jrowberg/keyglove/controller/arduino/keyglove/keyglove.cpp

// Keyglove Controller source code - Main setup/loop controller implementations
// 2015-07-03 by Jeff Rowberg <jeff@rowberg.net>

/* ============================================
Controller code is placed under the MIT license
Copyright (c) 2015 Jeff Rowberg

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
THE SOFTWARE IS PROVIDED "AS IS", WITHOUT WARRANTY OF ANY KIND, EXPRESS OR
IMPLIED, INCLUDING BUT NOT LIMITED TO THE WARRANTIES OF MERCHANTABILITY,
FITNESS FOR A PARTICULAR PURPOSE AND NONINFRINGEMENT. IN NO EVENT SHALL THE
AUTHORS OR COPYRIGHT HOLDERS BE LIABLE FOR ANY CLAIM, DAMAGES OR OTHER
LIABILITY, WHETHER IN AN ACTION OF CONTRACT, TORT OR OTHERWISE, ARISING FROM,
OUT OF OR IN CONNECTION WITH THE SOFTWARE OR THE USE OR OTHER DEALINGS IN
THE SOFTWARE.
===============================================
*/

/**
 * @file keyglove.cpp
 * @brief Main setup/loop controller implementations
 * @author Jeff Rowberg
 * @date 2015-07-03
 *
 * This is the main entry point and program flow control code for the entire
 * Keyglove Arduino firmware project, including the setup() and loop()
 * functions.
 *
 * Normally it is not necessary to edit this file.
 */

// CORE
#include "keyglove.h"

// BOARD
#include "support_board.h"

// COMMUNICATION PROTOCOL
#include "support_protocol.h"

// TOUCH SENSOR DETECTION LOGIC
#include "support_touch.h"

// FEEDBACK
#if (KG_FEEDBACK > 0)
    #include "support_feedback.h"
#endif

// MOTION
#if (KG_MOTION > 0)
    #include "support_motion.h"
#endif

// BLUETOOTH SUPPORT
#if (KG_HOSTIF & HG_HOSTIF_BT2_SPP) || (KG_HOSTIF & KG_HOSTIF_BT2_HID) || (KG_HOSTIF & KG_HOSTIF_BT2_RAWHID) || (KG_HOSTIF & KG_HOSTIF_BT2_IAP)
    #include "support_bluetooth.h"
#endif

// HUMAN INPUT DEVICE
#if (KG_HID & KG_HID_KEYBOARD)
    #include "support_hid_keyboard.h"
#endif
#if (KG_HID & KG_HID_MOUSE)
    #include "support_hid_mouse.h"
#endif

// USE THIS FILE TO IMPLEMENT ANY AUTONOMOUS BEHAVIOUR, SUCH AS ENABLING BLUETOOTH ON BOOT
#include "application.h"

volatile uint8_t keyglove100Hz = 0;         ///< Flag for 100Hz hardware timer interrupt
uint8_t keygloveTick = 0;                   ///< Fast 100Hz counter, increments every ~10ms and loops at 100
uint32_t keygloveTock = 0;                  ///< Slow 1Hz counter (a.k.a. "uptime"), increments every 100 ticks and loops at 2^32 (~4 billion)
//uint32_t keygloveTickTime = 0;              ///< Benchmark testing "end" reference timestamp
//uint32_t keygloveTickTime0 = 0;             ///< Benchmark testing "start" reference timestamp

uint8_t keygloveSoftTimers = 0;             ///< Bitmask for defined scheduled timers (one-shot or repeating)
uint8_t keygloveSoftTimersRepeat = 0;       ///< Bitmask for which scheduled timers are repeating
uint16_t keygloveSoftTimerInterval[8];      ///< Interval for each defined timer (units are 10ms)
uint32_t keygloveSoftTimerSec[8];           ///< Next "second" (tock) to execute each timer
uint8_t keygloveSoftTimer10ms[8];           ///< Next 10ms (tick) to execute each timer (w/corresponding second)

volatile uint8_t keygloveBatteryInterrupt;  ///< Flag for battery status change interrupt
volatile uint8_t keygloveBatteryStatus;     ///< Battery status signal container for post-interrupt processing
uint8_t keygloveBatteryLevel;               ///< Battery charge level (0-100)

/**
 * @brief Microcontroller initial setup routine
 *
 * Runs on power-on or reset, and again if `system_reset` BGAPI command is
 * received.
 */
void setup() {
    #if (KG_HOSTIF & HG_HOSTIF_BT2_SPP) || (KG_HOSTIF & KG_HOSTIF_BT2_HID) || (KG_HOSTIF & KG_HOSTIF_BT2_RAWHID) || (KG_HOSTIF & KG_HOSTIF_BT2_IAP)
        if (systemResetFlags & 0x01) {
            // reset Bluetooth module
            kg_cmd_bluetooth_reset();
            systemResetFlags &= ~(0x01);
        }
    #endif

    // reset runtime counters
    keygloveTick = 0;
    keygloveTock = 0;

    // BOARD
    setup_board();

    // COMMUNICATION PROTOCOL
    setup_protocol();

    // CUSTOM APPLICATION
    setup_application();

    // send system_boot event
    uint8_t payload[7] = {
        KG_FIRMWARE_VERSION_MAJOR,
        KG_FIRMWARE_VERSION_MINOR,
        KG_FIRMWARE_VERSION_PATCH,
        KG_BUILD_TIMESTAMP & 0xFF,
        (KG_BUILD_TIMESTAMP >> 8) & 0xFF,
        (KG_BUILD_TIMESTAMP >> 16) & 0xFF,
        (KG_BUILD_TIMESTAMP >> 24) & 0xFF
    };
    skipPacket = 0;
    if (kg_evt_system_boot) skipPacket = kg_evt_system_boot(KG_FIRMWARE_VERSION_MAJOR, KG_FIRMWARE_VERSION_MINOR, KG_FIRMWARE_VERSION_PATCH, KG_PROTOCOL_VERSION, KG_BUILD_TIMESTAMP);
    if (!skipPacket) send_keyglove_packet(KG_PACKET_TYPE_EVENT, 7, KG_PACKET_CLASS_SYSTEM, KG_PACKET_ID_EVT_SYSTEM_BOOT, payload);

    // CORE TOUCH SENSOR LOGIC
    setup_touch();

    // FEEDBACK
    #if (KG_FEEDBACK & KG_FEEDBACK_BLINK)
        setup_feedback_blink();
    #endif
    #if (KG_FEEDBACK & KG_FEEDBACK_PIEZO)
        setup_feedback_piezo();
    #endif
    #if (KG_FEEDBACK & KG_FEEDBACK_VIBRATE)
        setup_feedback_vibrate();
    #endif
    #if (KG_FEEDBACK & KG_FEEDBACK_RGB)
        setup_feedback_rgb();
    #endif

    // MOTION
    #if (KG_MOTION & KG_MOTION_MPU6050_HAND)
        setup_motion_mpu6050_hand();
    #endif

    // HOST INTERFACE
    #if (KG_HOSTIF & HG_HOSTIF_BT2_SPP) || (KG_HOSTIF & KG_HOSTIF_BT2_HID) || (KG_HOSTIF & KG_HOSTIF_BT2_RAWHID) || (KG_HOSTIF & KG_HOSTIF_BT2_IAP)
        setup_hostif_bt2();
    #endif

    // HUMAN INPUT DEVICE
    #if (KG_HID & KG_HID_KEYBOARD)
        setup_hid_keyboard();
    #endif
    #if (KG_HID & KG_HID_MOUSE)
        setup_hid_mouse();
    #endif

    // send system_ready event
    skipPacket = 0;
    if (kg_evt_system_ready) skipPacket = kg_evt_system_ready();
    if (!skipPacket) send_keyglove_packet(KG_PACKET_TYPE_EVENT, 0, KG_PACKET_CLASS_SYSTEM, KG_PACKET_ID_EVT_SYSTEM_READY, 0);
}

/**
 * @brief Microcontroller infinite loop routine
 *
 * This routine loops forever while the microcontroller is running. It is
 * responsible for checking on touch status, motion sensor status, and generally
 * everything else which does not rely strictly on hardware interrupts to
 * operate. Even some interrupt-related code is found here, since the interrupt
 * handlers typically just set a flag which causes this code to process the
 * event, so that the actual longer-running execution does not block any other
 * interrupts from occuring.
 */
void loop() {
    // check for incoming protocol data
    check_incoming_protocol_data();

    // check for 100Hz tick (i.e. every 10ms)
    if (keyglove100Hz) {
        keyglove100Hz = 0;
        //keygloveTickTime += micros() - keygloveTickTime0;
        //keygloveTickTime0 = micros();
        
        // update touch status
        update_touch();

        // update feedback settings
        #if (KG_FEEDBACK & KG_FEEDBACK_BLINK)
            update_feedback_blink();
        #endif // KG_FEEDBACK_BLINK
        #if (KG_FEEDBACK & KG_FEEDBACK_RGB)
            update_feedback_rgb();
        #endif // KG_FEEDBACK_RGB
        #if (KG_FEEDBACK & KG_FEEDBACK_PIEZO)
            update_feedback_piezo();
        #endif // KG_FEEDBACK_PIEZO
        #if (KG_FEEDBACK & KG_FEEDBACK_VIBRATE)
            update_feedback_vibrate();
        #endif // KG_FEEDBACK_VIBRATE

        // check for 100 ticks and reset counter (should be every 1 second)
        keygloveTick++;
        if (keygloveTick == 100) {
            //keygloveTickTime = 0;
            keygloveTick = 0;
            keygloveTock++;

            // read 0x04 SOC register from MAX17048 battery gauge to check for change
            uint8_t newBat;
            I2Cdev::readByte(0x36, 0x04, &newBat);
            newBat = min(100, max(0, newBat));
            
            if (newBat != keygloveBatteryLevel) {
                // percentage changed, trigger "interrupt" behavior below
                // TODO: CHANGE THIS TO USE THE /ALRT PIN ON MAX17048
                keygloveBatteryInterrupt = 1;
            }
        }

        // check for soft timer ticks
        for (uint8_t handle = 0; keygloveSoftTimers >> handle; handle++) {
            if ((keygloveSoftTimers >> handle) & 1) {
                if (keygloveSoftTimerSec[handle] == keygloveTock && keygloveSoftTimer10ms[handle] == keygloveTick) {
                    if ((keygloveSoftTimersRepeat >> handle) & 1) {
                        // reschedule on the same interval, since it's a repeating timer
                        keygloveSoftTimerSec[handle] = keygloveTock + (keygloveSoftTimerInterval[handle] / 100);
                        keygloveSoftTimer10ms[handle] = keygloveTick + (keygloveSoftTimerInterval[handle] % 100);
                        if (keygloveSoftTimer10ms[handle] > 99) {
                            keygloveSoftTimer10ms[handle] -= 100;
                            keygloveSoftTimerSec[handle]++;
                        }
                    } else {
                        // stop this timer
                        keygloveSoftTimers &= ~(1 << handle);
                    }
                    // send system_battery_timer_tick event
                    uint8_t payload[6] = {
                        handle,
                        (uint8_t)(keygloveTock & 0xFF),
                        (uint8_t)((keygloveTock >> 8) & 0xFF),
                        (uint8_t)((keygloveTock >> 16) & 0xFF),
                        (uint8_t)((keygloveTock >> 24) & 0xFF),
                        keygloveTick
                    };
                    skipPacket = 0;
                    if (kg_evt_system_timer_tick) skipPacket = kg_evt_system_timer_tick(handle, keygloveTock, keygloveTick);
                    if (!skipPacket) send_keyglove_packet(KG_PACKET_TYPE_EVENT, 6, KG_PACKET_CLASS_SYSTEM, KG_PACKET_ID_EVT_SYSTEM_TIMER_TICK, payload);
                }
            }
        }
    } else if (touchOn) {
        // update touch status instantly for low-latency when any are active
        update_touch();
    }

    // check for battery interrupt (status changed)
    if (keygloveBatteryInterrupt) {
        keygloveBatteryInterrupt = 0;

        // read 0x04 SOC register from MAX17048 battery gauge
        I2Cdev::readByte(0x36, 0x04, &keygloveBatteryLevel);
        keygloveBatteryLevel = min(100, max(0, keygloveBatteryLevel));

        // update battery presence bit
        //if (rawBat > 100) keygloveBatteryStatus |= 0x80;    // battery present
        //else keygloveBatteryStatus &= 0x7F;                 // battery not present

        // send system_battery_status event
        uint8_t payload[2] = {
            keygloveBatteryStatus,
            keygloveBatteryLevel
        };
        skipPacket = 0;
        if (kg_evt_system_battery_status) skipPacket = kg_evt_system_battery_status(keygloveBatteryStatus, keygloveBatteryLevel);
        if (!skipPacket) send_keyglove_packet(KG_PACKET_TYPE_EVENT, 2, KG_PACKET_CLASS_SYSTEM, KG_PACKET_ID_EVT_SYSTEM_BATTERY_STATUS, payload);
    }
    
    // MOTION
    #if (KG_MOTION & KG_MOTION_MPU6050_HAND)
        // check for available motion data from MPU-6050 on back of hand
        if (mpuHandInterrupt) {
            mpuHandInterrupt = false; // clear the flag so we don't read again until the next interrupt
            update_motion_mpu6050_hand();
        }
    #endif
    
    // send any queued packets
    send_keyglove_queue();
}
