jrowberg/keyglove/controller/arduino/keyglove/support_protocol.cpp

// Keyglove controller source code - KGAPI protocol core implementations
// 2015-07-03 by Jeff Rowberg <jeff@rowberg.net>

/* ============================================
Controller code is placed under the MIT license
Copyright (c) 2015 Jeff Rowberg

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
THE SOFTWARE IS PROVIDED "AS IS", WITHOUT WARRANTY OF ANY KIND, EXPRESS OR
IMPLIED, INCLUDING BUT NOT LIMITED TO THE WARRANTIES OF MERCHANTABILITY,
FITNESS FOR A PARTICULAR PURPOSE AND NONINFRINGEMENT. IN NO EVENT SHALL THE
AUTHORS OR COPYRIGHT HOLDERS BE LIABLE FOR ANY CLAIM, DAMAGES OR OTHER
LIABILITY, WHETHER IN AN ACTION OF CONTRACT, TORT OR OTHERWISE, ARISING FROM,
OUT OF OR IN CONNECTION WITH THE SOFTWARE OR THE USE OR OTHER DEALINGS IN
THE SOFTWARE.
===============================================
*/

/**
 * @file support_protocol.cpp
 * @brief KGAPI protocol core implementations
 * @author Jeff Rowberg
 * @date 2015-07-03
 *
 * This file implements the structure behind the Keyglove binary API protocol.
 * The incoming data stream parsing routines, error detection, timeout handling,
 * packet queuing, and packet sending functionality is all here. A few core API
 * commands and events are also implemented here. Subsystem-specific API packets
 * are defined and implemented elsewhere.
 *
 * Normally it is not necessary to edit this file.
 */

#include "keyglove.h"
#include "support_board.h"
#include "support_protocol.h"
 
#if KG_HOSTIF & KG_HOSTIF_USB_RAWHID
    uint8_t rxRawHIDPacket[USB_RAWHID_RX_SIZE];     ///< Outgoing raw HID report buffer
    uint8_t txRawHIDPacket[USB_RAWHID_TX_SIZE];     ///< Incoming raw HID report buffer
#endif

uint16_t rxByte;            ///< Container for incoming byte (actually WORD but the high byte is for .read() error checking)
uint8_t *rxPacket;          ///< Dynamic buffer for incoming KGAPI data
uint16_t rxPacketSize;      ///< Current size of container for received packet buffer
uint16_t rxPacketLength;    ///< Full length in bytes of received packet (may be less than rxPacketSize)
uint32_t packetStartTime;   ///< Incoming command packet timeout detection reference

uint8_t *txQueue;           ///< Dynamic buffer for TX packet queue
uint16_t txQueueSize;       ///< Allocated memory for the TX queue
uint16_t txQueueLength;     ///< Number of bytes used in the TX queue

bool inBinPacket = false;   ///< Indicates whether we have started parsing a binary packet or not
uint8_t binDataLength;      ///< Expected size of incoming binary data (should be rxPacketLength - 4)
uint8_t skipPacket = 0;     ///< Global var to control whether event packet will be skipped due to custom handler

uint8_t lastCommandInterfaceNum;    ///< Source interface number of last incoming command packet

uint8_t systemResetFlags = 0; ///< Controls what to reset when we use "system_reset" API command

/**
 * @brief Initialize protocol buffers and BGAPI parser
 */
void setup_protocol() {
    // allocate RX packet buffer on fresh boot
    if (rxPacketSize == 0 || rxPacket == 0) {
        rxPacketSize = 32;
        rxPacket = (uint8_t *)malloc(rxPacketSize);
        rxPacketLength = 0;
    }
}

/**
 * @brief Set RX packet state back to "empty" state
 * @return Number of bytes in packet buffer at time of reset
 */
uint16_t reset_keyglove_rx_packet() {
    uint16_t prevLength = rxPacketLength;
    inBinPacket = false;
    rxPacketLength = 0;
    return prevLength;
}

/**
 * @brief Parse the next incoming KGAPI protocol byte
 * @param[in] inputByte Incoming byte to parse
 */
void protocol_parse(uint8_t inputByte) {
    if (rxPacketLength + 1 == rxPacketSize) {
        rxPacketSize += 32;
        rxPacket = (uint8_t *)realloc(rxPacket, rxPacketSize);
        if (!rxPacket) {
            // failed to reallocate to new chunk of memory
            // this should NEVER happen, but if it does, I want to know
            uint8_t payload[2] = { KG_PROTOCOL_ERROR_NULL_POINTER & 0xFF, KG_PROTOCOL_ERROR_NULL_POINTER >> 8 };
            skipPacket = 0;
            if (kg_evt_protocol_error) skipPacket = kg_evt_protocol_error(KG_PROTOCOL_ERROR_NULL_POINTER);
            if (!skipPacket) send_keyglove_packet(KG_PACKET_TYPE_EVENT, 2, KG_PACKET_CLASS_PROTOCOL, KG_PACKET_ID_EVT_PROTOCOL_ERROR, payload);
            return;
        }
    }
    if (!inBinPacket && inputByte == KG_PACKET_TYPE_COMMAND) { // "bait" byte, 0xC0
        packetStartTime = millis();
        inBinPacket = true;
        rxPacket[0] = inputByte;
        rxPacketLength = 1; // initialize buffer length to include only 1st header byte (so far)
        binDataLength = 0;
    } else if (inBinPacket && rxPacketLength == 1) { // data length byte
        binDataLength = inputByte;
        if (binDataLength > 250) {
            // error (data payload too long)
            uint8_t payload[2] = { KG_PROTOCOL_ERROR_BAD_LENGTH, 0x00 };
            skipPacket = 0;
            if (kg_evt_protocol_error) skipPacket = kg_evt_protocol_error(payload[0]);
            if (!skipPacket) send_keyglove_packet(KG_PACKET_TYPE_EVENT, 2, KG_PACKET_CLASS_PROTOCOL, KG_PACKET_ID_EVT_PROTOCOL_ERROR, payload);
            inBinPacket = false;
            rxPacketLength = 0;
        } else {
            rxPacket[rxPacketLength++] = inputByte;
        }
    } else {
        rxPacket[rxPacketLength++] = inputByte;
        if (inBinPacket && rxPacketLength - 4 == binDataLength) {
            // process packet that just came in, passing to appropriate main handler
            uint8_t protocol_error = 0;

            // filter incoming packets for custom behavior
            if (filter_incoming_keyglove_packet(rxPacket) == 0) {
                switch (rxPacket[2]) {
                    //case KG_PACKET_CLASS_PROTOCOL:

                    case KG_PACKET_CLASS_SYSTEM:
                        protocol_error = process_protocol_command_system(rxPacket);
                        break;
    
                    case KG_PACKET_CLASS_TOUCH:
                        protocol_error = process_protocol_command_touch(rxPacket);
                        break;
    
                    #if KG_MOTION > 0
                        case KG_PACKET_CLASS_MOTION:
                            protocol_error = process_protocol_command_motion(rxPacket);
                            break;
                    #endif
    
                    #if KG_FEEDBACK > 0
                        case KG_PACKET_CLASS_FEEDBACK:
                            protocol_error = process_protocol_command_feedback(rxPacket);
                            break;
                    #endif
    
                    #if KG_FLEX > 0
                        case KG_PACKET_CLASS_FLEX:
                            protocol_error = process_protocol_command_flex(rxPacket);
                            break;
                    #endif
    
                    #if KG_PRESSURE > 0
                        case KG_PACKET_CLASS_PRESSURE:
                            protocol_error = process_protocol_command_pressure(rxPacket);
                            break;
                    #endif
    
                    #if KG_TOUCHSET > 0
                        case KG_PACKET_CLASS_TOUCHSET:
                            protocol_error = process_protocol_command_touchset(rxPacket);
                            break;
                    #endif
    
                    #if (KG_HOSTIF & HG_HOSTIF_BT2_SPP) || (KG_HOSTIF & KG_HOSTIF_BT2_RAWHID) || (KG_HOSTIF & KG_HOSTIF_BT2_IAP)
                        case KG_PACKET_CLASS_BLUETOOTH:
                            protocol_error = process_protocol_command_bluetooth(rxPacket);
                            break;
                    #endif
    
                    default:
                        // check for custom protocol, will return KG_PROTOCOL_ERROR_INVALID_COMMAND if no matches
                        protocol_error = KG_PROTOCOL_ERROR_INVALID_COMMAND;
                        break;
                }

                // check for errors (e.g. unhandled, bad arguments, etc.)
                if (protocol_error) {
                    // check for custom protocol, will return KG_PROTOCOL_ERROR_INVALID_COMMAND if no matches
                    protocol_error = process_protocol_command_custom(rxPacket);

                    // if we still have an error, then there is no custom functionality implemented for this class/ID combination
                    if (protocol_error) {
                        uint8_t payload[2] = { protocol_error, 0x00 };
                        skipPacket = 0;
                        if (kg_evt_protocol_error) skipPacket = kg_evt_protocol_error(payload[0]);
                        if (!skipPacket) send_keyglove_packet(KG_PACKET_TYPE_EVENT, 2, KG_PACKET_CLASS_PROTOCOL, KG_PACKET_ID_EVT_PROTOCOL_ERROR, payload);
                    }
                }
            }

            // reset packet status/length
            reset_keyglove_rx_packet();
        }
    }
}

/**
 * @brief Check all relevant interfaces for any incoming protocol data
 * @return Result, zero for success or non-zero for error
 */
uint8_t check_incoming_protocol_data() {
    #if KG_HOSTIF & KG_HOSTIF_USB_SERIAL
        // read available data from USB virtual serial
        if (interfaceUSBSerialReady && (interfaceUSBSerialMode & KG_INTERFACE_MODE_INCOMING_API) != 0) {
            while ((rxByte = USBSerial.read()) < 256) {
                lastCommandInterfaceNum = KG_INTERFACENUM_USB_SERIAL;
                protocol_parse((uint8_t)rxByte);
            }
        }
    #endif

    #if KG_HOSTIF & KG_HOSTIF_USB_RAWHID
        // read raw HID data over USB
        if (interfaceUSBRawHIDReady && (interfaceUSBRawHIDMode & KG_INTERFACE_MODE_INCOMING_API) != 0) {
            int8_t bytes = RawHID.recv(rxRawHIDPacket, 0);
            if (bytes > 0) {
                lastCommandInterfaceNum = KG_INTERFACENUM_USB_RAWHID;
                for (int8_t i = 0; i < rxRawHIDPacket[0]; i++) protocol_parse(rxRawHIDPacket[i + 1]);
            }
        }
    #endif

    #if (KG_HOSTIF & HG_HOSTIF_BT2_SPP) || (KG_HOSTIF & KG_HOSTIF_BT2_HID) || (KG_HOSTIF & KG_HOSTIF_BT2_RAWHID) || (KG_HOSTIF & KG_HOSTIF_BT2_IAP)
        // see if there is any data to deal with from Bluetooth
        bluetooth_check_incoming_protocol_data();
    #endif

    // check for protocol timeout condition
    if (inBinPacket && (millis() - packetStartTime) > KG_PROTOCOL_RX_TIMEOUT) {
        // error (data payload too long)
        uint8_t payload[2] = { KG_PROTOCOL_ERROR_PACKET_TIMEOUT, 0x00 };
        skipPacket = 0;
        if (kg_evt_protocol_error) skipPacket = kg_evt_protocol_error(payload[0]);
        if (!skipPacket) send_keyglove_packet(KG_PACKET_TYPE_EVENT, 2, KG_PACKET_CLASS_PROTOCOL, KG_PACKET_ID_EVT_PROTOCOL_ERROR, payload);
        inBinPacket = false;
        rxPacketLength = 0;
    }

    return 0;
}

/**
 * @brief Send a special log message (from RAM) out the main serial interface
 * @param[in] level Log level
 * @param[in] length Number of bytes in message
 * @param[in] message Message to send (normal variable in RAM)
 * @return Result, zero for success or non-zero for error
 */
uint8_t send_keyglove_log(uint8_t level, uint8_t length, const char *message) {
    uint8_t beginning[] = { 0x80, (uint8_t)(length + 1), 0xFF, 0xFF, level };
    Serial.write(beginning, 5);
    Serial.println((const char *)message);
    return 0;
}

/**
 * @brief Send a special log message (from flash) out the main serial interface
 * @param[in] level Log level
 * @param[in] length Number of bytes in message
 * @param[in] message Message to send (from flash)
 * @return Result, zero for success or non-zero for error
 */
uint8_t send_keyglove_log(uint8_t level, uint8_t length, const __FlashStringHelper *message) {
    uint8_t beginning[] = { 0x80, (uint8_t)(length + 1), 0xFF, 0xFF, level };
    Serial.write(beginning, 5);
    Serial.println((const __FlashStringHelper *)message);
    return 0;
}

/**
 * @brief Add an outgoing packet (response or event) to the queue to send later
 * @param[in] packetType Type of packet to send
 * @param[in] payloadLength Number of bytes in data payload (0 or more)
 * @param[in] packetClass Packet class ID byte
 * @param[in] packetId Packet command ID byte
 * @param[in] payload Payload data byte array
 * @return Result, zero for success or non-zero for error
 */
uint8_t queue_keyglove_packet(uint8_t packetType, uint8_t payloadLength, uint8_t packetClass, uint8_t packetId, uint8_t *payload) {
    uint8_t packetLength = payloadLength + 4;
    if (txQueueSize == 0) {
        if (!(txQueue = (uint8_t *)malloc(384))) {
            return 1; // couldn't allocate block of memory
        }
        txQueueSize = 384;
    } else if (txQueueSize + packetLength > txQueueSize) {
        if (!(txQueue = (uint8_t *)realloc(txQueue, txQueueSize + packetLength + 64))) {
            return 2; // couldn't re-allocate bigger block of memory
        }
        txQueueSize += packetLength + 64;
    }
    txQueue[txQueueLength++] = packetType;
    txQueue[txQueueLength++] = payloadLength;
    txQueue[txQueueLength++] = packetClass;
    txQueue[txQueueLength++] = packetId;
    if (payloadLength) {
        memcpy(txQueue + txQueueLength, payload, payloadLength);
        txQueueLength += payloadLength;
    }
    return 0;
}

/**
 * @brief Send an outgoing packet (response or event) immediately
 * @param[in] packetType Type of packet to send
 * @param[in] payloadLength Number of bytes in data payload (0 or more)
 * @param[in] packetClass Packet class ID byte
 * @param[in] packetId Packet command ID byte
 * @param[in] payload Payload data byte array
 * @return Result, zero for success or non-zero for error
 */
uint8_t send_keyglove_packet(uint8_t packetType, uint8_t payloadLength, uint8_t packetClass, uint8_t packetId, uint8_t *payload) {
    // validate payload length
    if ((payload == NULL && payloadLength > 0) || payloadLength > 250) {
        // payload specified but not provided, or too long
        return 1;
    }
    
    // filter outgoing packets for custom behavior
    if (filter_outgoing_keyglove_packet(&packetType, &payloadLength, &packetClass, &packetId, payload)) return 255;

    // allocate and check full packet buffer
    uint8_t *buffer = (uint8_t *)malloc(4 + payloadLength);
    if (buffer == 0) {
        // couldn't allocate packet buffer...uh oh
        return 2;
    }

    // certain outgoing packets should only be sent on one specific interface, the last one which was used
    uint8_t specificInterface = (packetType != KG_PACKET_TYPE_EVENT || packetClass == KG_PACKET_CLASS_PROTOCOL);

    buffer[0] = packetType;
    buffer[1] = payloadLength;
    buffer[2] = packetClass;
    buffer[3] = packetId;
    if (payloadLength) memcpy(buffer + 4, payload, payloadLength);
    uint8_t length = 4 + payloadLength;

    #if KG_HOSTIF & KG_HOSTIF_USB_SERIAL
        if (!specificInterface || lastCommandInterfaceNum == KG_INTERFACENUM_USB_SERIAL) {
            // send packet out over wired serial (USB virtual serial)
            if (interfaceUSBSerialReady && (interfaceUSBSerialMode & KG_INTERFACE_MODE_OUTGOING_API) != 0) {
                USBSerial.write((const uint8_t *)buffer, length); // packet data
            }
        }
    #endif

    #if KG_HOSTIF & KG_HOSTIF_USB_RAWHID
        if (!specificInterface || lastCommandInterfaceNum == KG_INTERFACENUM_USB_RAWHID) {
            // send packet out over wired custom HID interface (USB raw HID)
            // 64-byte packets, formatted where byte 0 is [0-64] and bytes 1-63 are data
            if (interfaceUSBRawHIDReady && (interfaceUSBRawHIDMode & KG_INTERFACE_MODE_OUTGOING_API) != 0) {
                //int8_t bytes;
                for (uint8_t i = 0; i < length; i += (USB_RAWHID_TX_SIZE - 1)) {
                    memset(txRawHIDPacket, 0, USB_RAWHID_TX_SIZE);
                    txRawHIDPacket[0] = min(USB_RAWHID_TX_SIZE - 1, length - i);
                    for (uint8_t j = 0; j < (USB_RAWHID_TX_SIZE - 1); j++) {
                        if (i + j >= length) break;
                        txRawHIDPacket[j + 1] = buffer[i + j];
                    }
                    /*bytes = */ RawHID.send(txRawHIDPacket, 2);
                }
            }
        }
    #endif

    #if (KG_HOSTIF & HG_HOSTIF_BT2_SPP) || (KG_HOSTIF & KG_HOSTIF_BT2_HID) || (KG_HOSTIF & KG_HOSTIF_BT2_RAWHID) || (KG_HOSTIF & KG_HOSTIF_BT2_IAP)
        // send packet via Bluetooth if necessary
        bluetooth_send_keyglove_packet_buffer(buffer, length, specificInterface);
    #endif

    // KG_HID_KEYBOARD and KG_HID_MOUSE are handled elsewhere and deal with other kinds of data
    
    // tidy up!
    free(buffer);

    return 0;
}

/**
 * @brief Check for and send next available queued packet (if any)
 * @return Number of bytes still used in outgoing queue
 * @see queue_keyglove_packet()
 */
uint16_t send_keyglove_queue() {
    // check for queued packets
    if (txQueueLength) {
        send_keyglove_packet(txQueue[0], txQueue[1], txQueue[2], txQueue[3], txQueue + 4);
        if (txQueueLength > (uint16_t)(txQueue[1] + 4)) {
            // queue has more left, so move it into position
            txQueueLength -= (txQueue[1] + 4);
            memmove(txQueue, txQueue + (txQueue[1] + 4), txQueueLength);
        } else {
            // queue is empty, free up the memory
            txQueueLength = 0;
            txQueueSize = 0;
            free(txQueue);
        }
    }
    return txQueueLength;
}

/* 0x01 */ uint8_t (*kg_evt_protocol_error)(uint16_t code) = 0;
