jrowberg/keyglove/controller/arduino/keyglove/support_hid_mouse.cpp

// Keyglove controller source code - HID mouse helper function implementations
// 2014-11-07 by Jeff Rowberg <jeff@rowberg.net>

/* ============================================
Controller code is placed under the MIT license
Copyright (c) 2014 Jeff Rowberg

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
THE SOFTWARE IS PROVIDED "AS IS", WITHOUT WARRANTY OF ANY KIND, EXPRESS OR
IMPLIED, INCLUDING BUT NOT LIMITED TO THE WARRANTIES OF MERCHANTABILITY,
FITNESS FOR A PARTICULAR PURPOSE AND NONINFRINGEMENT. IN NO EVENT SHALL THE
AUTHORS OR COPYRIGHT HOLDERS BE LIABLE FOR ANY CLAIM, DAMAGES OR OTHER
LIABILITY, WHETHER IN AN ACTION OF CONTRACT, TORT OR OTHERWISE, ARISING FROM,
OUT OF OR IN CONNECTION WITH THE SOFTWARE OR THE USE OR OTHER DEALINGS IN
THE SOFTWARE.
===============================================
*/

/**
 * @file support_hid_mouse.cpp
 * @brief HID mouse helper function implementations
 * @author Jeff Rowberg
 * @date 2014-11-07
 *
 * This file provides supporting code for translating motion into mouse movement
 * data, and for sending this HID mouse data to a connected wired or wireless
 * host. This is only relevant if you have enabled normal HID support over USB
 * or Bluetooth.
 *
 * Normally it is not necessary to edit this file.
 */

#include "keyglove.h"
#include "support_board.h"
#include "support_hid_mouse.h"
#include "support_motion.h"
#include "support_bluetooth2_iwrap.h"

uint8_t hidMouseDown = 0;   ///< Mouse buttons currently down

int8_t hidMouseDX;          ///< Mouse cursor X axis movement delta
int8_t hidMouseDY;          ///< Mouse cursor Y axis movement delta
int8_t hidMouseDZ;          ///< Mouse cursor Z axis movement delta (3D-only)
int8_t hidScrollDX;         ///< Horizontal scroll movement delta
int8_t hidScrollDY;         ///< Vertical scroll movement delta

uint8_t opt_hid_mouse_invert_x = 0;                 ///< OPTION: Invert mouse x movements
uint8_t opt_hid_mouse_invert_y = 1;                 ///< OPTION: Invert mouse y movements
uint8_t opt_hid_mouse_invert_z = 0;                 ///< OPTION: Invert mouse z movements

mouse_movement_mode_t opt_hid_mouse_mode = MOUSE_MODE_OFF;      ///< OPTION: Mouse cursor movement mode
scroll_movement_mode_t opt_hid_scroll_mode = SCROLL_MODE_OFF;   ///< OPTION: Scroll movement mode

float opt_hid_mouse_scale_mode1[] = { 1, 1 };       ///< OPTION: Speed scale [x,y] for mode 1 (tilt-velocity)
float opt_hid_mouse_scale_mode2[] = { 1, 1 };       ///< OPTION: Speed scale [x,y] for mode 2 (tilt-position)
float opt_hid_mouse_scale_mode3[] = { 1, 1 };       ///< OPTION: Speed scale [x,y] for mode 3 (movement-position)
float opt_hid_mouse_scale_mode4[] = { 1, 1, 1 };    ///< OPTION: Speed scale [x,y,z] for mode 4 (3D)

/**
 * @brief Initialize HID mouse behavior
 */
void setup_hid_mouse() {
    // zero all relative movements
    hidMouseDX = hidMouseDY = hidMouseDZ = 0;
    hidScrollDX = hidScrollDY = 0;
}

/**
 * @brief Update mouse movements if necessary, called at 100Hz from loop()
 */
void update_hid_mouse() {
    #if KG_MOTION > 0
        switch (opt_hid_mouse_mode) {
            case MOUSE_MODE_OFF:
            case MOUSE_MODE_MAX:
                // do nothing for these values (explicit case avoids compiler warning)
                break;
            case MOUSE_MODE_TILT_VELOCITY:
                hidMouseDX += ((gv.y < 0) ? -pow(-(float)gv.y/30, 1.3)*3 : pow((float)gv.y/30, 1.3)*3) - ((gv.z < 0) ? -pow(-(float)gv.z/30, 1.3)*3 : pow((float)gv.z/30, 1.3)*3);
                hidMouseDY += (gv.x < 0) ? -pow(-(float)gv.x/30, 1.3)*3 : pow((float)gv.x/30, 1.3)*3;
                break;
            case MOUSE_MODE_TILT_POSITION:
                hidMouseDX = ((gv.y < 0) ? -pow(-(float)gv.y/30, 1.3)*3 : pow((float)gv.y/30, 1.3)*3) - ((gv.z < 0) ? -pow(-(float)gv.z/30, 1.3)*3 : pow((float)gv.z/30, 1.3)*3);
                hidMouseDY = (gv.x < 0) ? -pow(-(float)gv.x/30, 1.3)*3 : pow((float)gv.x/30, 1.3)*3;
                break;
            case MOUSE_MODE_MOVEMENT_POSITION:
                #if (KG_FUSION > 0)
                    hidMouseDX = apFrame.x * opt_hid_mouse_scale_mode4[0];
                    hidMouseDY = apFrame.y * opt_hid_mouse_scale_mode4[1];
                #else
                    hidMouseDX = aa.x * opt_hid_mouse_scale_mode4[0];
                    hidMouseDY = aa.y * opt_hid_mouse_scale_mode4[1];
                #endif
                break;
            case MOUSE_MODE_3D:
                #if (KG_FUSION > 0)
                    hidMouseDX = apFrame.x * opt_hid_mouse_scale_mode4[0];
                    hidMouseDY = apFrame.y * opt_hid_mouse_scale_mode4[1];
                    hidMouseDZ = apFrame.z * opt_hid_mouse_scale_mode4[2];
                #else
                    hidMouseDX = aa.x * opt_hid_mouse_scale_mode4[0];
                    hidMouseDY = aa.y * opt_hid_mouse_scale_mode4[1];
                    hidMouseDZ = aa.z * opt_hid_mouse_scale_mode4[2];
                #endif
                break;
        }
        switch (opt_hid_scroll_mode) {
            case SCROLL_MODE_OFF:
            case SCROLL_MODE_MAX:
                // do nothing for these values (explicit case avoids compiler warning)
                break;
            case SCROLL_MODE_TILT_VELOCITY: // gyro
                break;
            case SCROLL_MODE_TILT_POSITION: // gyro
                hidScrollDY -= ((float)gv.y < 0) ? -sqrt(-(float)gv.y / 30) : sqrt((float)gv.y / 30);
                break;
            case SCROLL_MODE_MOVEMENT_POSITION: // accel
                break;
        }
    #endif

    if (opt_hid_mouse_mode > 0 && (hidMouseDX != 0 || hidMouseDY != 0 || hidMouseDZ != 0)) {
        if (opt_hid_mouse_invert_x == 1) hidMouseDX = -hidMouseDX;
        if (opt_hid_mouse_invert_y == 1) hidMouseDY = -hidMouseDY;
        if (opt_hid_mouse_invert_z == 1) hidMouseDZ = -hidMouseDZ;
        #if KG_HOSTIF & KG_HOSTIF_USB_HID
            if (hidMouseDZ > 0) Mouse.move(hidMouseDX, hidMouseDY, hidMouseDZ);
            else Mouse.move(hidMouseDX, hidMouseDY);
        #endif /* KG_HOSTIF_USB_HID */
        #if KG_HOSTIF & KG_HOSTIF_BT2_HID
            if (hidMouseDZ > 0) BTMouse.move(hidMouseDX, hidMouseDY, hidMouseDZ, 0);
            else BTMouse.move(hidMouseDX, hidMouseDY);
        #endif /* KG_HOSTIF_BT2_HID */
        #if KG_HOSTIF & KG_HOSTIF_R400_HID
            if (hidMouseDZ > 0) RX400.move(hidMouseDX, hidMouseDY, hidMouseDZ);
            else RX400.move(hidMouseDX, hidMouseDY);
        #endif /* KG_HOSTIF_R400_HID */
    }
    if (opt_hid_scroll_mode > 0 && hidScrollDY != 0) {
        if (opt_hid_mouse_invert_y == 1) hidMouseDY = -hidMouseDY;
        #if KG_HOSTIF & KG_HOSTIF_USB_HID
            Mouse.scroll(hidScrollDY);
        #endif /* KG_HOSTIF_USB_HID */
        #if KG_HOSTIF & KG_HOSTIF_BT2_HID
            BTMouse.scroll(hidScrollDY, 0);
        #endif /* KG_HOSTIF_BT2_HID */
        #if KG_HOSTIF & KG_HOSTIF_R400_HID
            RX400.scroll(hidScrollDY);
        #endif /* KG_HOSTIF_R400_HID */
    }
}

/**
 * @brief Turn on mouse for cursor movement or scrolling
 * @param[in] mode Which operational mode to turn on
 * @see MOUSE_ACTION_MOVE
 * @see MOUSE_ACTION_SCROLL
 */
void mouse_on(uint8_t mode) {
    #if KG_HID & KG_HID_MOUSE
        if (mode == MOUSE_ACTION_MOVE) {
            opt_hid_mouse_mode = MOUSE_MODE_TILT_POSITION;
        } else if (mode == MOUSE_ACTION_SCROLL) {
            opt_hid_scroll_mode = SCROLL_MODE_TILT_POSITION;
        }
        #ifdef ENABLE_ACCELEROMETER
            if (!activeAccelerometer) enable_motion_accelerometer();
        #endif
        #ifdef ENABLE_GYROSCOPE
            if (!activeGyroscope) enable_motion_gyroscope();
        #endif
        #ifdef ENABLE_ACCELGYRO
            if (!activeAccelGyro) enable_motion_accelgyro();
        #endif
    #endif
}

/**
 * @brief Turn off mouse to end cursor movement or scrolling
 * @param[in] mode Which operational mode to turn off
 * @see MOUSE_ACTION_MOVE
 * @see MOUSE_ACTION_SCROLL
 */
void mouse_off(uint8_t mode) {
    #if KG_HID & KG_HID_MOUSE
        if (mode == MOUSE_ACTION_MOVE) {
            opt_hid_mouse_mode = MOUSE_MODE_OFF;
        } else if (mode == MOUSE_ACTION_SCROLL) {
            opt_hid_scroll_mode = SCROLL_MODE_OFF;
        }
        #ifdef ENABLE_ACCELEROMETER
            if (activeAccelerometer) disable_motion_accelerometer();
        #endif
        #ifdef ENABLE_GYROSCOPE
            if (activeGyroscope) disable_motion_gyroscope();
        #endif
        #ifdef ENABLE_ACCELGYRO
            if (activeAccelGyro) disable_motion_accelgyro();
        #endif
    #endif
}

/**
 * @brief Send button-press (down) HID report
 * @param[in] button Mouse button bitmask
 * @see MOUSE_LEFT
 * @see MOUSE_RIGHT
 * @see MOUSE_MIDDLE
 */
void mouse_down(uint8_t button) {
    #if KG_HID & KG_HID_MOUSE
        hidMouseDown = hidMouseDown | button;
        #if KG_HOSTIF & KG_HOSTIF_USB_HID
            if (interfaceUSBHIDReady) {
                Mouse.set_buttons((hidMouseDown & 1) > 0 ? 1 : 0, (hidMouseDown & 2) > 0 ? 1 : 0, (hidMouseDown & 4) > 0 ? 1 : 0);
            }
        #endif /* KG_HOSTIF_USB_HID */
    #endif
}

/**
 * @brief Send button-release (up) HID report
 * @param[in] button Mouse button bitmask
 * @see MOUSE_LEFT
 * @see MOUSE_RIGHT
 * @see MOUSE_MIDDLE
 */
void mouse_up(uint8_t button) {
    #if KG_HID & KG_HID_MOUSE
        if ((hidMouseDown & button) > 0) {
            hidMouseDown -= button;
            #if KG_HOSTIF & KG_HOSTIF_USB_HID
                if (interfaceUSBHIDReady) {
                    Mouse.set_buttons((hidMouseDown & 1) > 0 ? 1 : 0, (hidMouseDown & 2) > 0 ? 1 : 0, (hidMouseDown & 4) > 0 ? 1 : 0);
                }
            #endif /* KG_HOSTIF_USB_HID */
        }
    #endif
}

/**
 * @brief Send button-click (down-up) HID reports
 * @param[in] button Mouse button bitmask
 * @see MOUSE_LEFT
 * @see MOUSE_RIGHT
 * @see MOUSE_MIDDLE
 */
void mouse_click(uint8_t button) {
    mouse_down(button);
    delay(5);
    mouse_up(button);
}
